estella-warwick/BumbleBox/box components/3d printed components/latch_key.stl

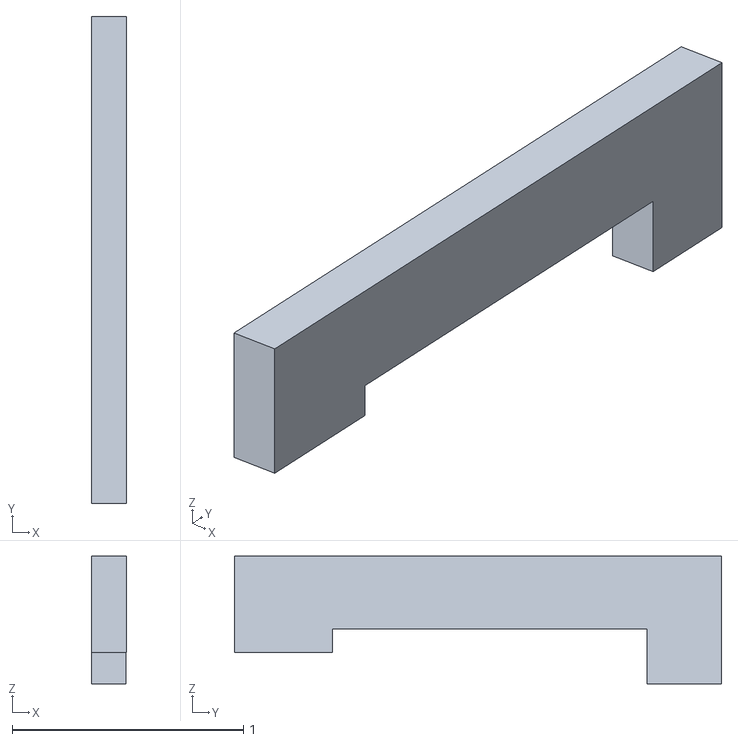
[picture p20: CAD file, 2023-11-07]
box components/3d printed components/latch_key.stl
0.15 x 2.11 x 0.554
