estella-warwick/BumbleBox/box components/acrylic sheet components/dxf files/wall.dxf

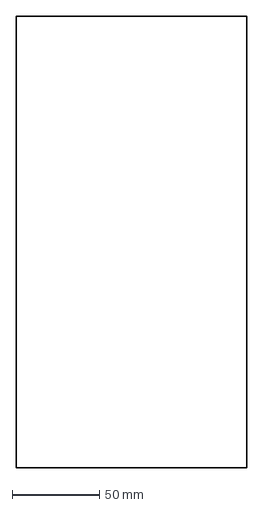
[picture p21: CAD file, 2024-01-31]
box components/acrylic sheet components/dxf files/wall.dxf
132.0 x 259.1 mm
