estella-warwick/BumbleBox/box components/3d printed components/entrance_inner_door.3mf

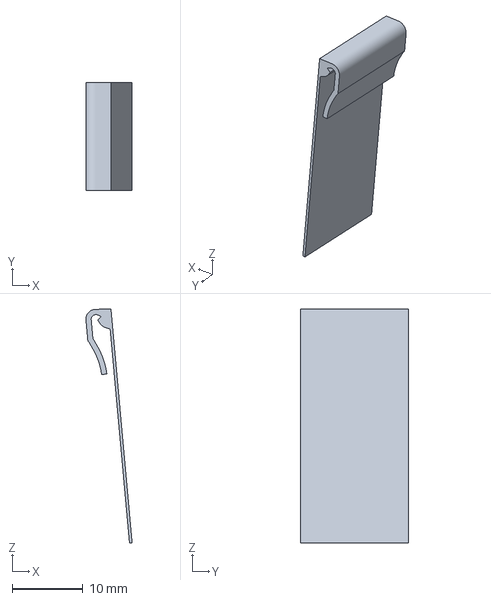
[picture p22: CAD file, 2023-11-07]
box components/3d printed components/entrance_inner_door.3mf
6.56 x 15.2 x 33.2 mm
