estella-warwick/BumbleBox/box components/acrylic sheet components/dxf files/diffuser_top_proto.dxf

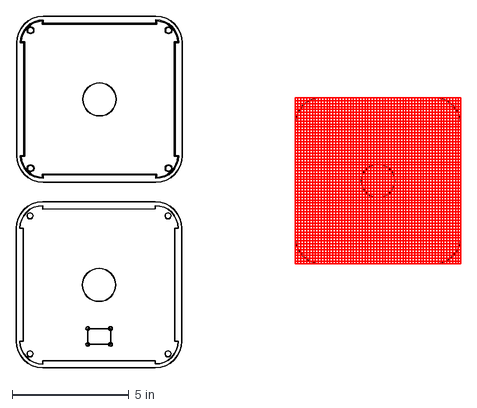
[picture p23: CAD file, 2023-11-07]
box components/acrylic sheet components/dxf files/diffuser_top_proto.dxf
19.0 x 15.0 in
