estella-warwick/BumbleBox/box components/3d printed components/box_foot.3mf

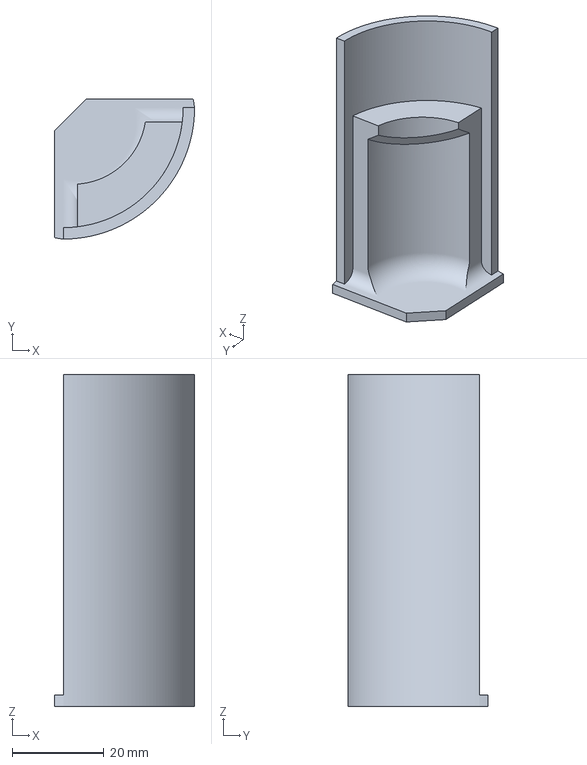
[picture p24: CAD file, 2023-11-07]
box components/3d printed components/box_foot.3mf
30.6 x 30.6 x 72.4 mm
