estella-warwick/BumbleBox/box components/acrylic sheet components/dxf files/access_door_wall.dxf

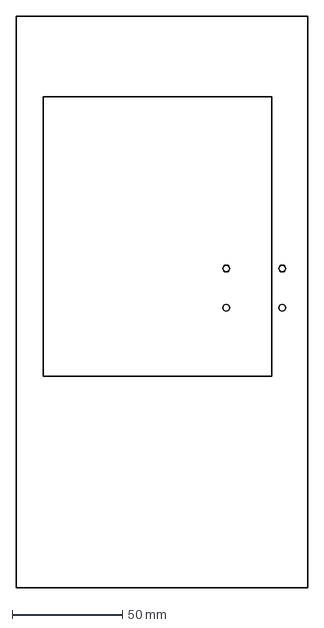
[picture p25: CAD file, 2023-11-07]
box components/acrylic sheet components/dxf files/access_door_wall.dxf
132.0 x 259.1 mm
