estella-warwick/BumbleBox/box components/3d printed components/outer_door.3mf

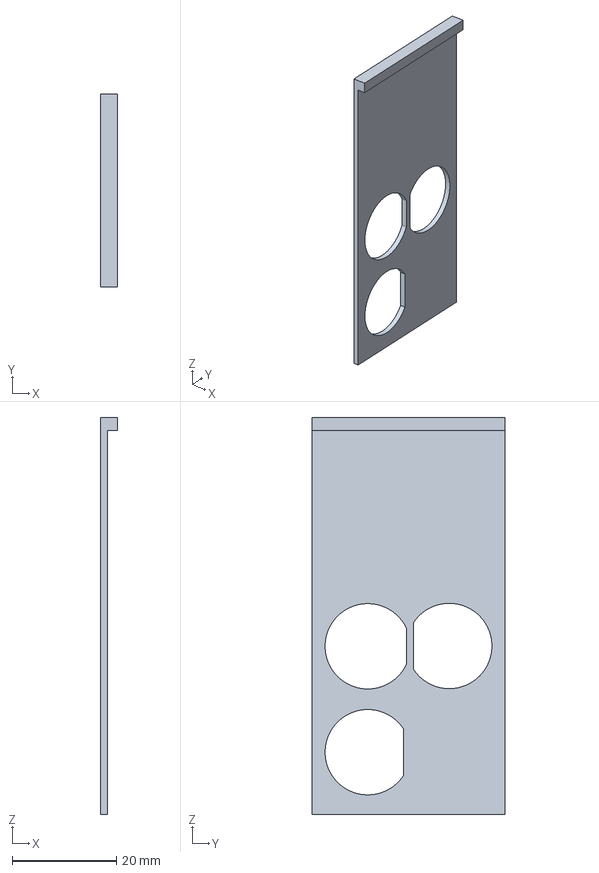
[picture p26: CAD file, 2023-11-07]
box components/3d printed components/outer_door.3mf
3.17 x 37.1 x 76.2 mm
