estella-warwick/BumbleBox/box components/3d printed components/imaging_top_side_innie.3mf

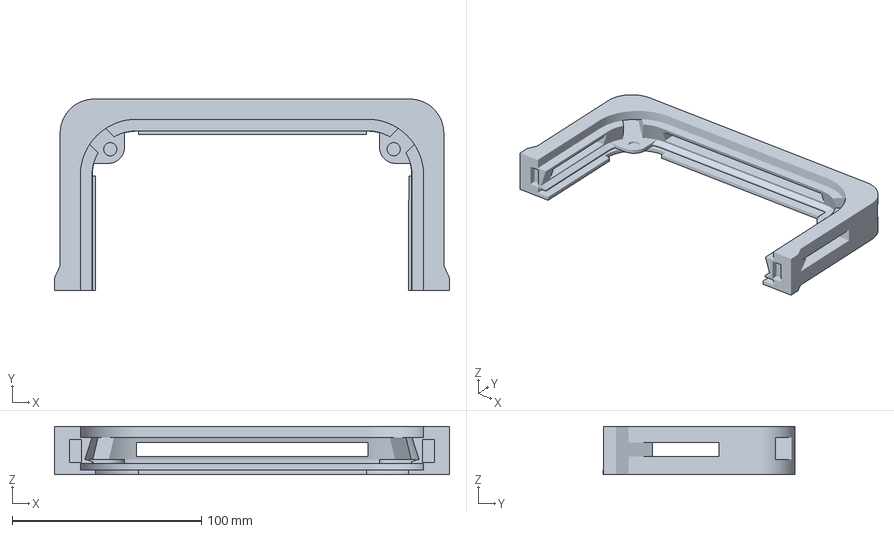
[picture p28: CAD file, 2023-11-07]
box components/3d printed components/imaging_top_side_innie.3mf
208.8 x 101.4 x 25.4 mm
