estella-warwick/BumbleBox/box components/3d printed components/custom_box_entrance.3mf

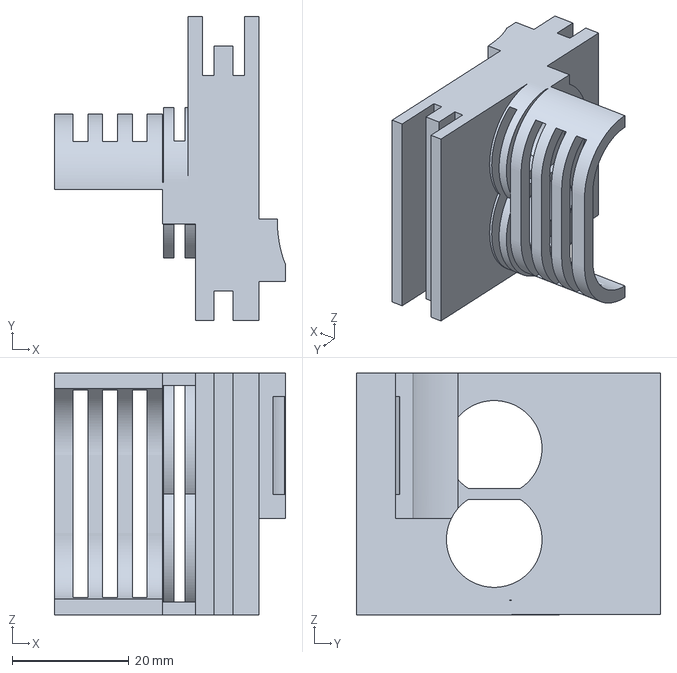
[picture p29: CAD file, 2023-11-07]
box components/3d printed components/custom_box_entrance.3mf
39.6 x 52.1 x 41.4 mm
