estella-warwick/BumbleBox/box components/3d printed components/imaging_top_side_outie.3mf

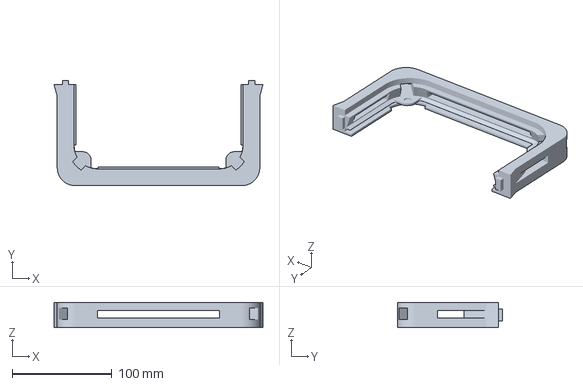
[picture p30: CAD file, 2023-11-07]
box components/3d printed components/imaging_top_side_outie.3mf
209.2 x 105.4 x 25.4 mm
