estella-warwick/BumbleBox/box components/3d printed components/latch.stl

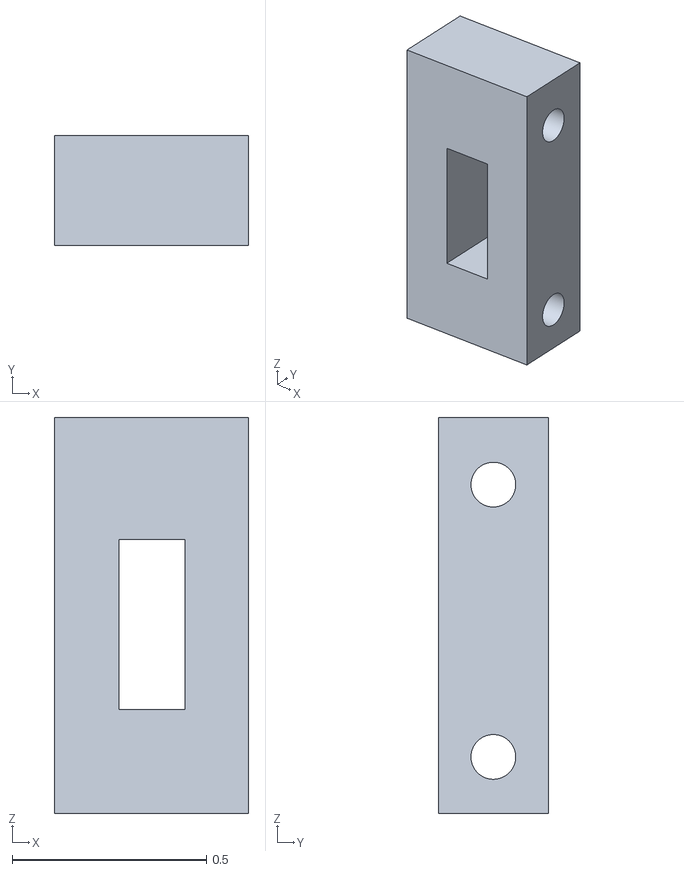
[picture p31: CAD file, 2023-11-07]
box components/3d printed components/latch.stl
0.5 x 0.283 x 1.02
