estella-warwick/BumbleBox/generate_nest_images.py

#import numpy as np
import cv2
#import skvideo.io
import os
#import zarr
import dask.array as da
import glob
import random
import datetime
from record_video import create_todays_folder #change this so that this function sits in this script, doesnt need to be imported from record_video
import setup
import socket
import argparse
import sys
import logging
import time
import gc

logging.basicConfig(filename='/home/pi/Desktop/BumbleBox/logs/log.log',encoding='utf-8',format='%(filename)s %(asctime)s: %(message)s', filemode='a', level=logging.DEBUG)
logger = logging.getLogger(__name__)
logger.setLevel(logging.DEBUG)

#generate Nest Images folder
def make_nest_images_dir():
    if not os.path.isdir(f'{setup.data_folder_path}/Nest Images'):
        print("Need to make nest folder!")
        try:
            os.makedirs(f'{setup.data_folder_path}/Nest Images')
            return 0, f'{setup.data_folder_path}/Nest Images'
		
        except Exception as e:
            print(e)
            print(e.args)
            print("Couldn't make today's folder for some reason... trying subprocess!")
            try:
                nest_folder_path = f'{setup.data_folder_path}/Nest Images'
                subprocess.call(['sudo', 'mkdir', '-p', nest_folder_path])
                return 0, nest_folder_path
            except:
                print(e)
                print(e.args)
                print("That didn't work either! Huh...")
                return 1, nest_folder_path
    else:
        return 0, f'{setup.data_folder_path}/Nest Images'

#alternative code for compiling pngs
def generate_nest_image(todays_folder_path, today, number_of_images, hostname, shuffle=True):
    
    ret, nestpath = make_nest_images_dir()
    files = []
    for file in glob.glob(f"{todays_folder_path}/*.png"):
        print(file)
        files.append(file)
    if shuffle==True:
        random.shuffle(files)
        
    total_frames = len(files)
    print(total_frames)
    
    if total_frames > number_of_images:
        total_frames = number_of_images
        files = files[:total_frames]
        
    file_dimensions = []
    index = 0
    print("Trying to read image file!")
    imgdata = cv2.imread(files[0])
    gray_img = cv2.cvtColor(imgdata, cv2.COLOR_RGB2GRAY)
    
    try:
        h,w,d = gray_img.shape
        print("Image is 3d")
        x = da.zeros((total_frames,h,w,d)).astype('uint8')
        print(f"empty image array shape: {x.shape}")
    except:
        h,w = gray_img.shape
        x = da.zeros((total_frames,h,w)).astype('uint8')
        print(f"empty image array shape: {x.shape}")
    #for file in first_set:
    
    
    for file in files:
        #filename = os.path.basename(filename)
        #fname, ext = os.path.splitext(filename)
        print(file)
        imgdata = cv2.imread(file)
        gray_img = cv2.cvtColor(imgdata, cv2.COLOR_RGB2GRAY)
        gray_img = gray_img.astype('uint8')
        #videodata = skvideo.io.vread(file)
        #f,h,w,d = videodata.shape
        try:
            h,w,d = gray_img.shape
            dims = (h,w,d)
            print(h,w,d)
            file_dimensions.append(dims)
            print(f"file dimensions: {file_dimensions[0]}")
            if dims != file_dimensions[0]:
                print('resizing')
                imgdata = cv2.resize(gray_img, (file_dimensions[0][1], file_dimensions[0][0]))
            print(gray_img.shape)
            x[index] = gray_img
            print("Got here")
            index += 1
        except Exception as e:
            print(e)
            #print('had a dimension issue, image not 3d')
            h,w = gray_img.shape
            file_dimensions.append((h,w))
            if h != file_dimensions[0][0] and w != file_dimensions[0][1]:
                gray_img = cv2.resize(gray_img, (file_dimensions[0][1], file_dimensions[0][0]))
            print(f'gray image shape: {gray_img.shape}. Empty frame shape: {x[index].shape}')
            try:
                x[index] = gray_img
            except:
                print("Skipping image, its dimensions arent the same as that of the first image in this randomized list")
            index += 1
            
    print("Computing image")
    a = da.median(x, axis=0)
    a1 = a.compute()
    
    print("Writing image")
    #cv2.imwrite(f'{todays_folder_path}/{hostname}-{today}-nest_image.png', final_image)
    cv2.imwrite(f'{todays_folder_path}/{hostname}-{today}-nest_image.png', a1)
    cv2.imwrite(f'{nestpath}/{hostname}-{today}-nest_image.png', a1)
    print("Image written!")
    logger.debug(f"Composite image written using {total_frames} images!")
    return total_frames

def main():
    
    start = time.time()
    
    parser = argparse.ArgumentParser(prog='Generate a composite nest image (from the images in todays folder) without bees in it! ')
    parser.add_argument('-p', '--data_folder_path', type=str, default=setup.data_folder_path, help='a path to the folder you want to collect data in. Default path is: /mnt/bumblebox/data/')
    parser.add_argument('-i', '--number_of_images', type=int, default=setup.number_of_images, help='the number of images you want to use to create your composite nest labelling image from todays images. The more you use, the longer this takes!')
    parser.add_argument('-sh', '--shuffle', type=bool, default=True, help='if shuffle is True, all the images from todays folder will be randomized so that this script isnt choosing just the earliest images from today. If you want images from a shorter timespan, choose this and a lower number of frames (youll have to do the time calculations yourself, based on how frequently recordings and images are generated and how many frames youve chosen. Default is True.')
    args = parser.parse_args()
    
    hostname = socket.gethostname()
    today = datetime.date.today()
    
    
    ret, todays_folder_path = create_todays_folder(args.data_folder_path)
    if ret == 1:
        print("Couldn't create todays folder to store data in. Exiting program. Sad!")
        return 1
    
    #run_via_cron = None
    
    if sys.stdout.isatty():
        print("Running from terminal")
        logger.debug("Running generate nest image script from terminal")
        #run_via_cron = False
        
        print(f"This is the generate_nest_images script! Im looking for images in:\n\n{todays_folder_path}\n\nThis is todays data folder.\nDo you want to use a different folder?")   
        print("\n")
        yes_or_no = input("Enter yes or no: ")
        
        while yes_or_no != "yes" and yes_or_no != "no":
            print("Do you want to use a different folder?")
            yes_or_no = input("Please enter either yes or no, all lowercase: ")
            
        if yes_or_no == "yes":
            print("Type the new path without a trailing \"/\" after the folder name - Example: /mnt/bumblebox/data/2023-10-23")
            todays_folder_path = input("Folder path: ")
            print(f"Using {todays_folder_path}. Moving on!")
        
        elif yes_or_no == "no":
            print("Moving on, then!")
        
        else:
            print("Type yes or no, all lowercase. Try again!")
            
        print(f"What do you want your new image filename to be? It will look like this: (computer hostname)-(your text here)-nest_image.png. Example: bumblebox-03-trial2_hr10-hr18-nest_image.png")
        today = input("Enter text: ")
        print(f"Filename: {hostname}-{today}-nest_image.png")

        
    else:
        logger.debug("Running nest image generation script via crontab")
        print("Running nest image generation script via crontab")
        #run_via_cron = True
    
    
    total_frames = generate_nest_image(todays_folder_path, today, args.number_of_images, hostname, shuffle=True)
    
    end = time.time()
    
    print(f"Creation of composite image took {round(end - start,2)} seconds for {total_frames} images.")
    logger.debug(f"Creation of composite image took {round(end - start,2)} seconds for {total_frames} images.")

if __name__ == '__main__':

    main()
    logging.shutdown()
